Ptr314/agat_boards/docs/IO9/Fg3.089.174_TO/p9008.jpg

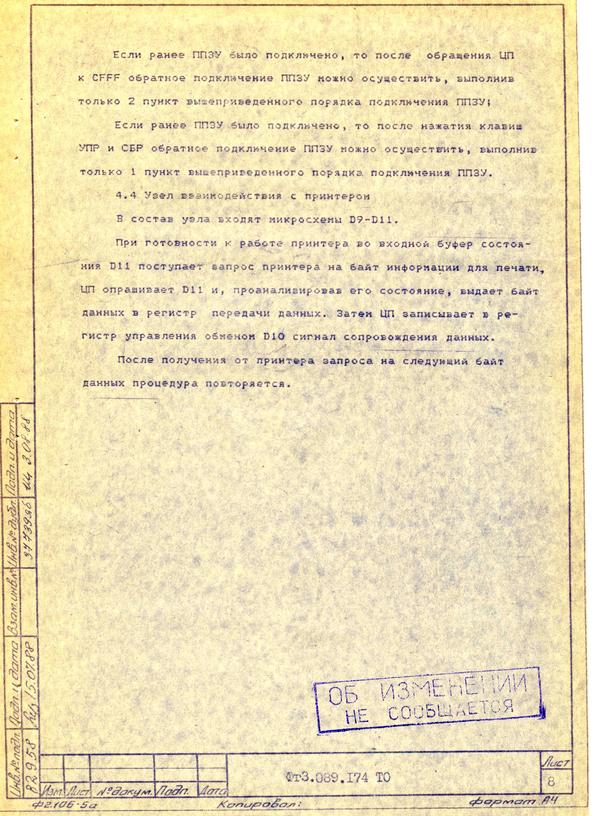
docs/IO9/Fg3.089.174_TO/p9008.jpg
